jguillen-lab/BFS9000/firmware/vial-qmk/keyboards/jguillen_lab/bfs9000/readme.md

# BFS9000

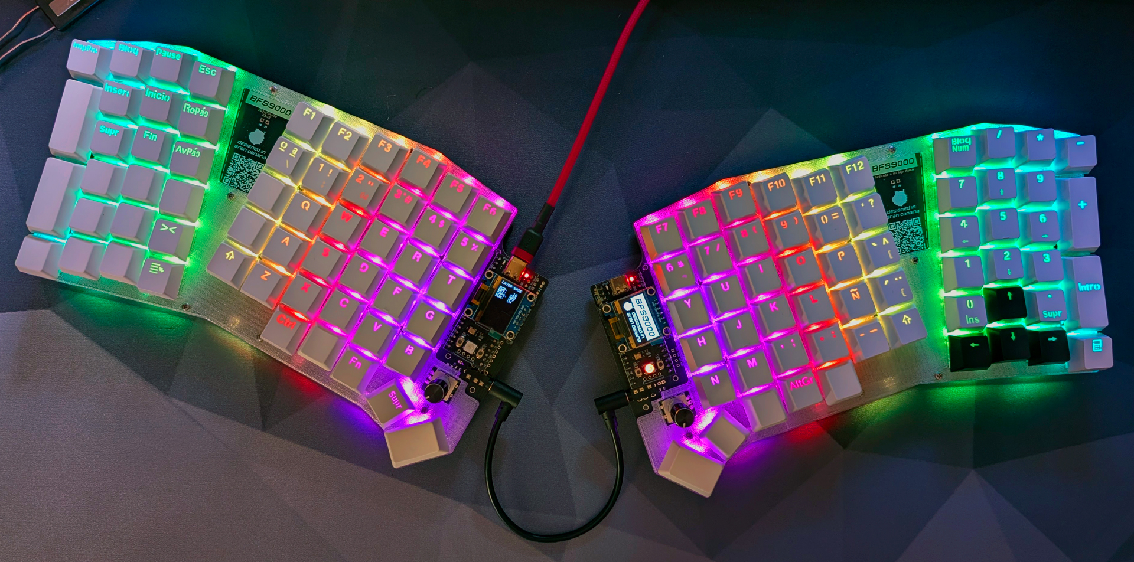
[picture p14: media/kbpic/000_no1.jpg]
BFS9000


BFS9000 is a custom split keyboard designed by Jesús Guillén. It runs QMK Firmware with Vial support and includes RGB Matrix lighting, OLED display support, combo/tap-dance features, and an Azoteq IQS5xx pointing device.

* Keyboard Maintainer: [Jesús Guillén](https://github.com/jguillen-lab)
* Hardware Supported: BFS9000 PCB
* Hardware Availability: [BFS9000 repository](https://github.com/jguillen-lab/BFS9000)

Make example for this keyboard, after setting up your build environment:

```
make jguillen_lab/bfs9000:default
```

Flashing example for this keyboard:

```
make jguillen_lab/bfs9000:default:flash
```

Vial keymap build example:

```
make jguillen_lab/bfs9000:vial
```

Vial keymap flashing example:

```
make jguillen_lab/bfs9000:vial:flash
```

See the [build environment setup](https://docs.qmk.fm/newbs_getting_started) and the [make instructions](https://docs.qmk.fm/newbs_building_firmware) for more information.
