jguillen-lab/BFS9000/media/keymap_es_ES.png

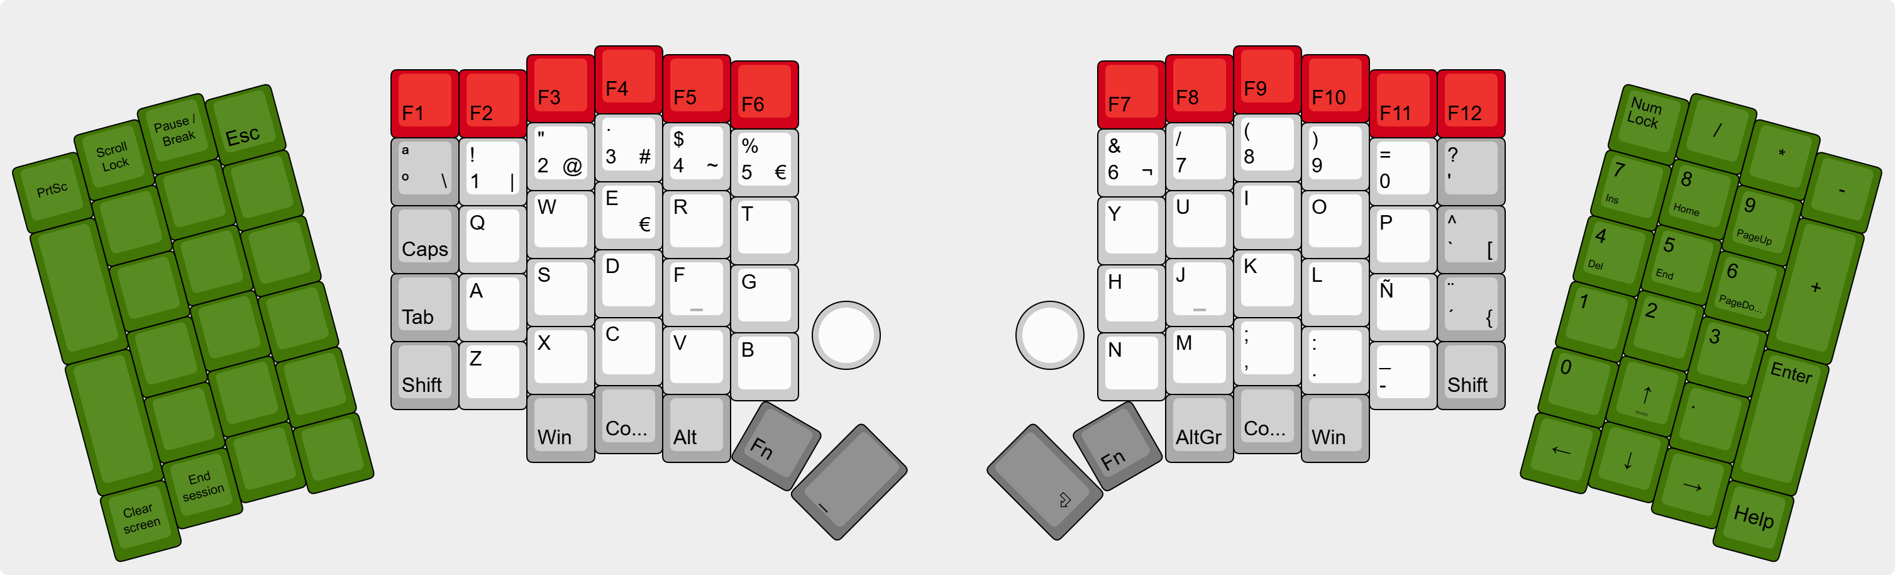
media/keymap_es_ES.png
