jguillen-lab/BFS9000/media/layouts/combinations.png

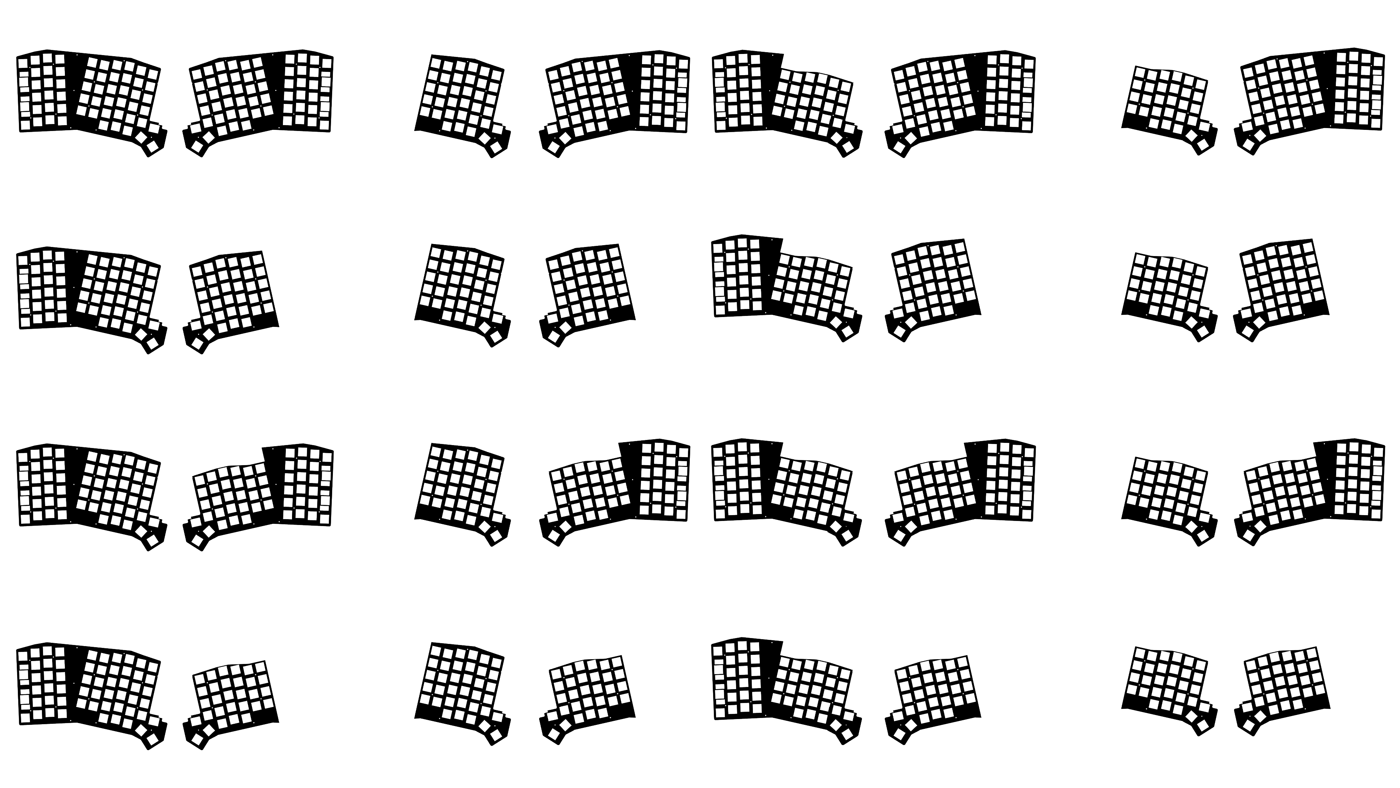
media/layouts/combinations.png
