jguillen-lab/BFS9000/media/layouts/full_left.png

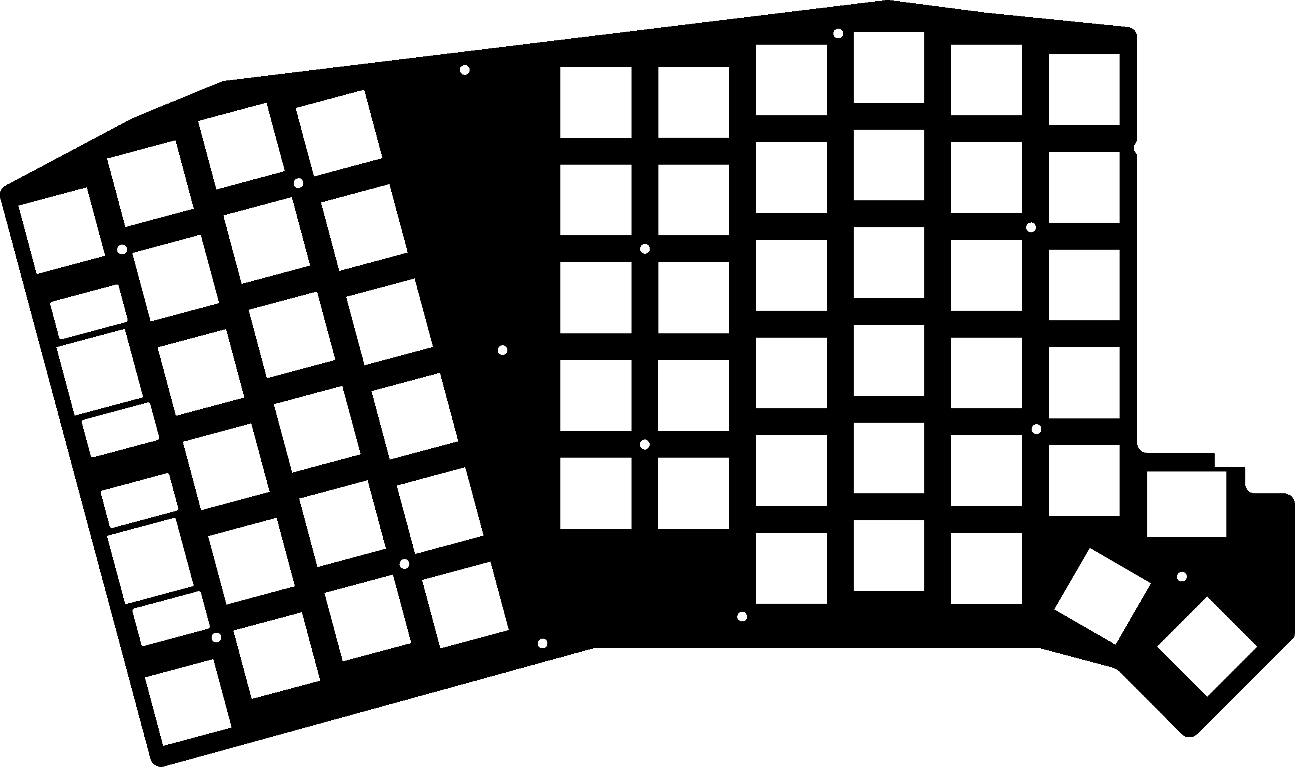
media/layouts/full_left.png
