jguillen-lab/BFS9000/media/layouts/full_right.png

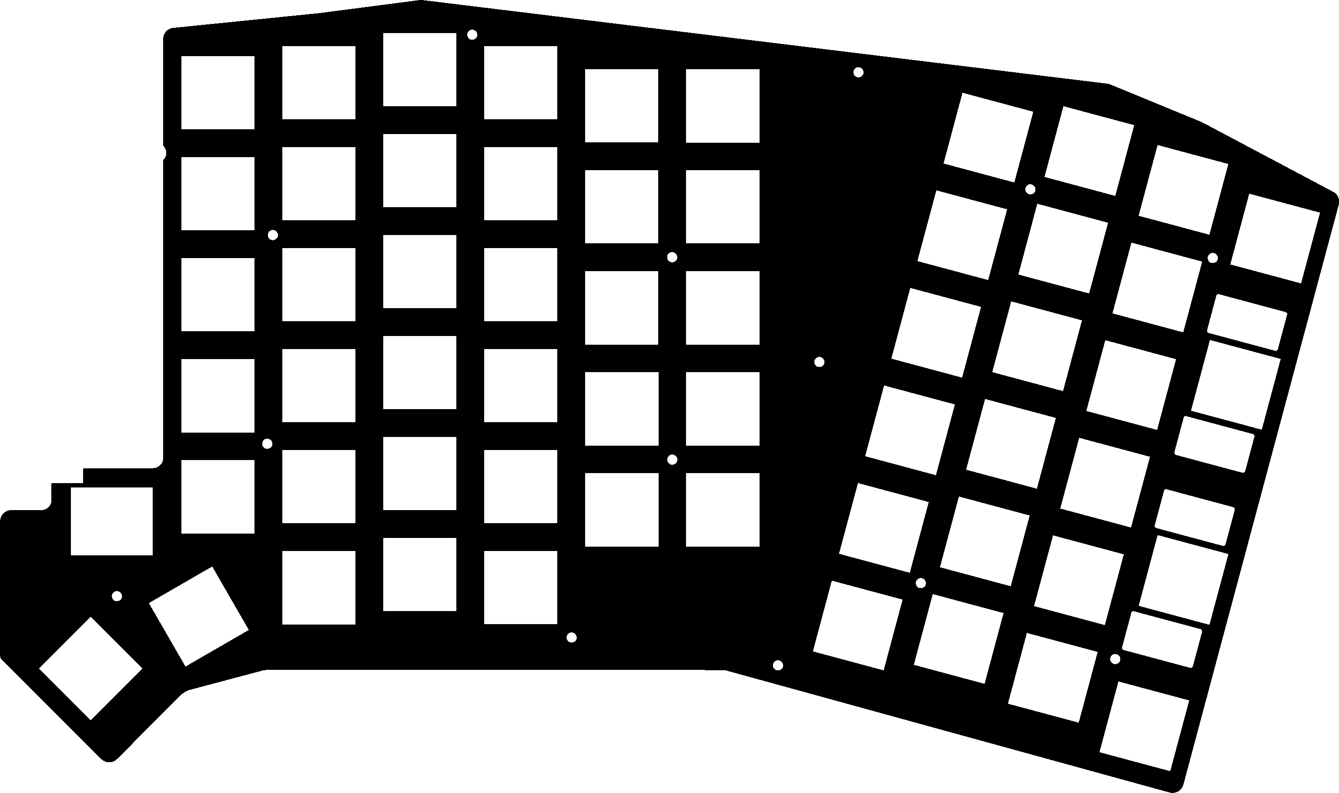
media/layouts/full_right.png
