jguillen-lab/BFS9000/media/layouts/main_left.png

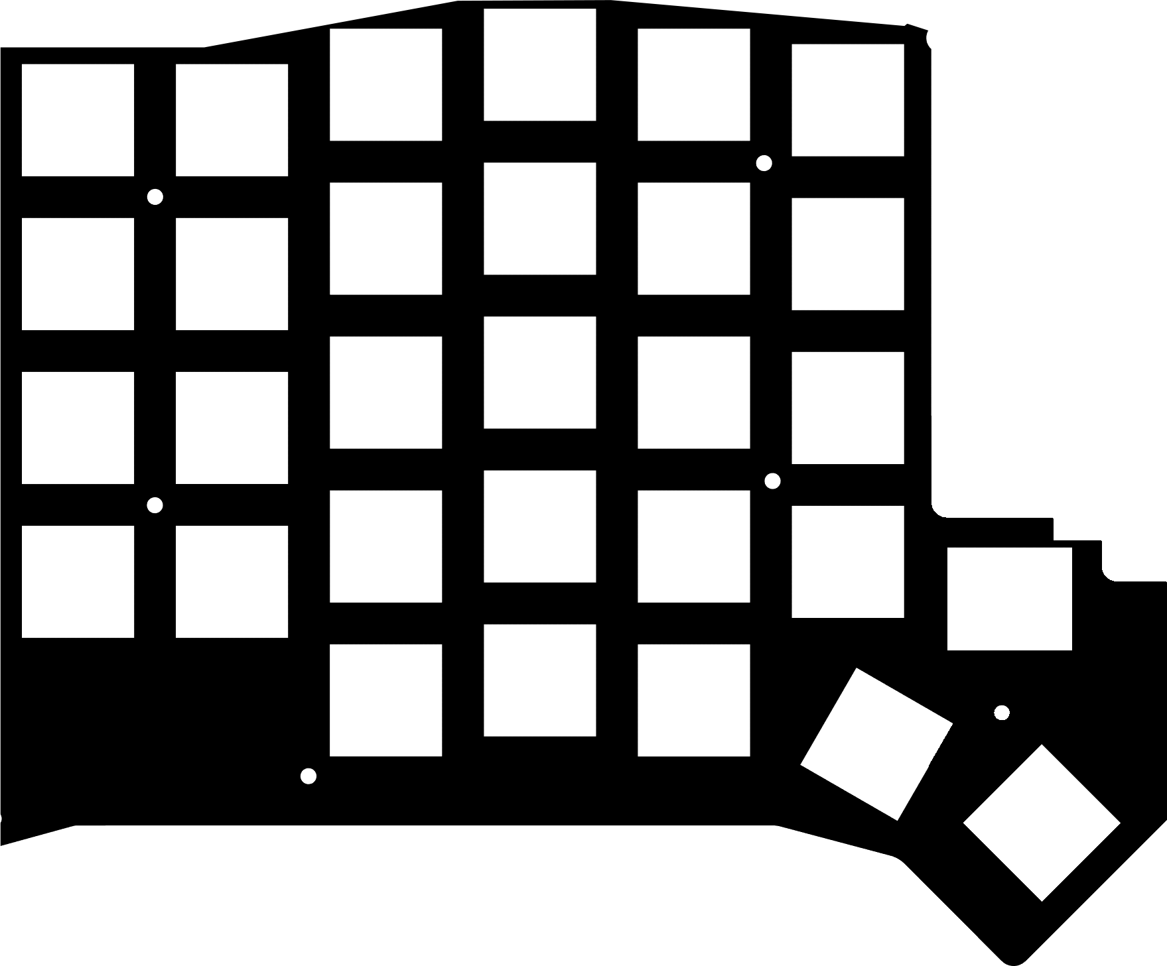
media/layouts/main_left.png
