jguillen-lab/BFS9000/media/layouts/main_right.png

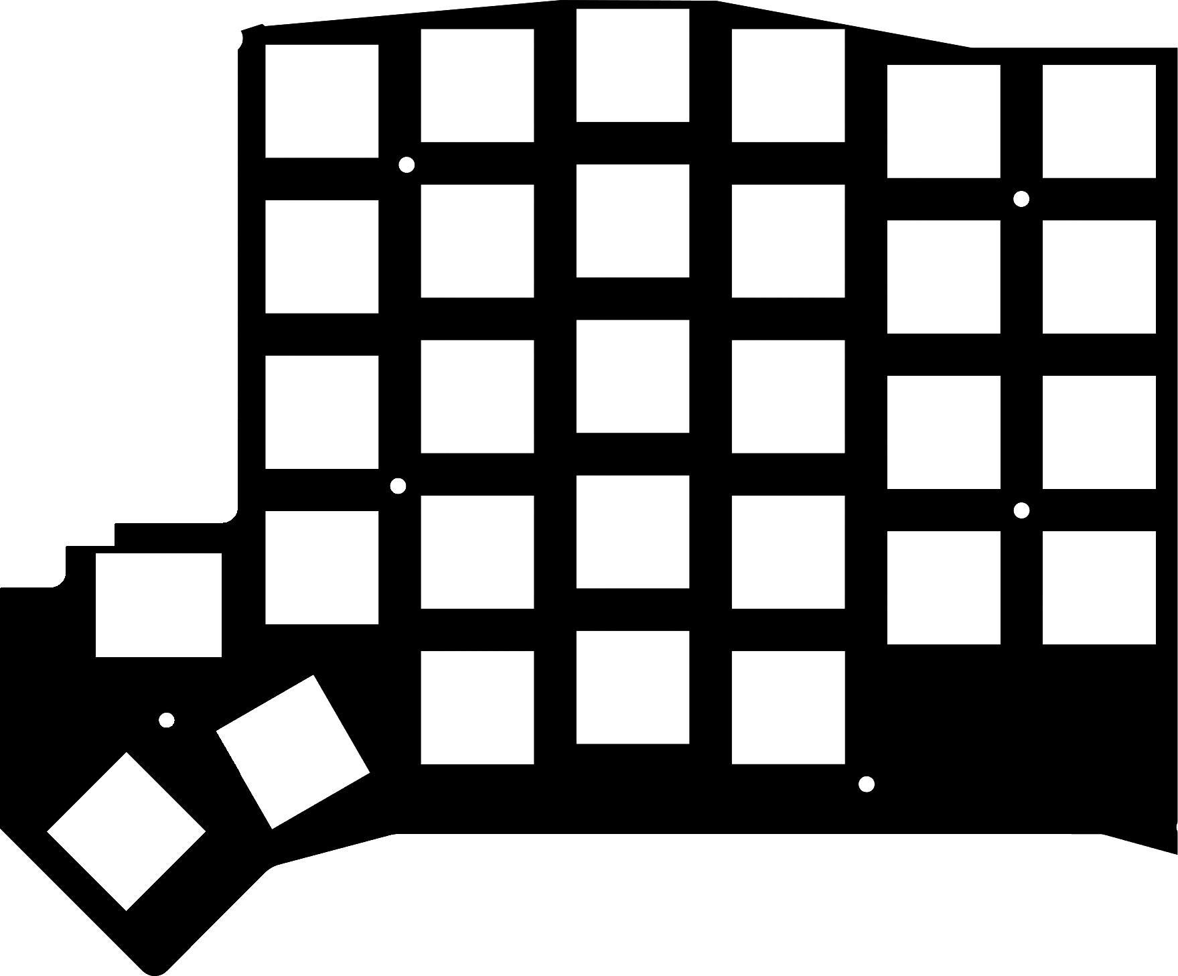
media/layouts/main_right.png
