jguillen-lab/BFS9000/media/layouts/main_side_right.png

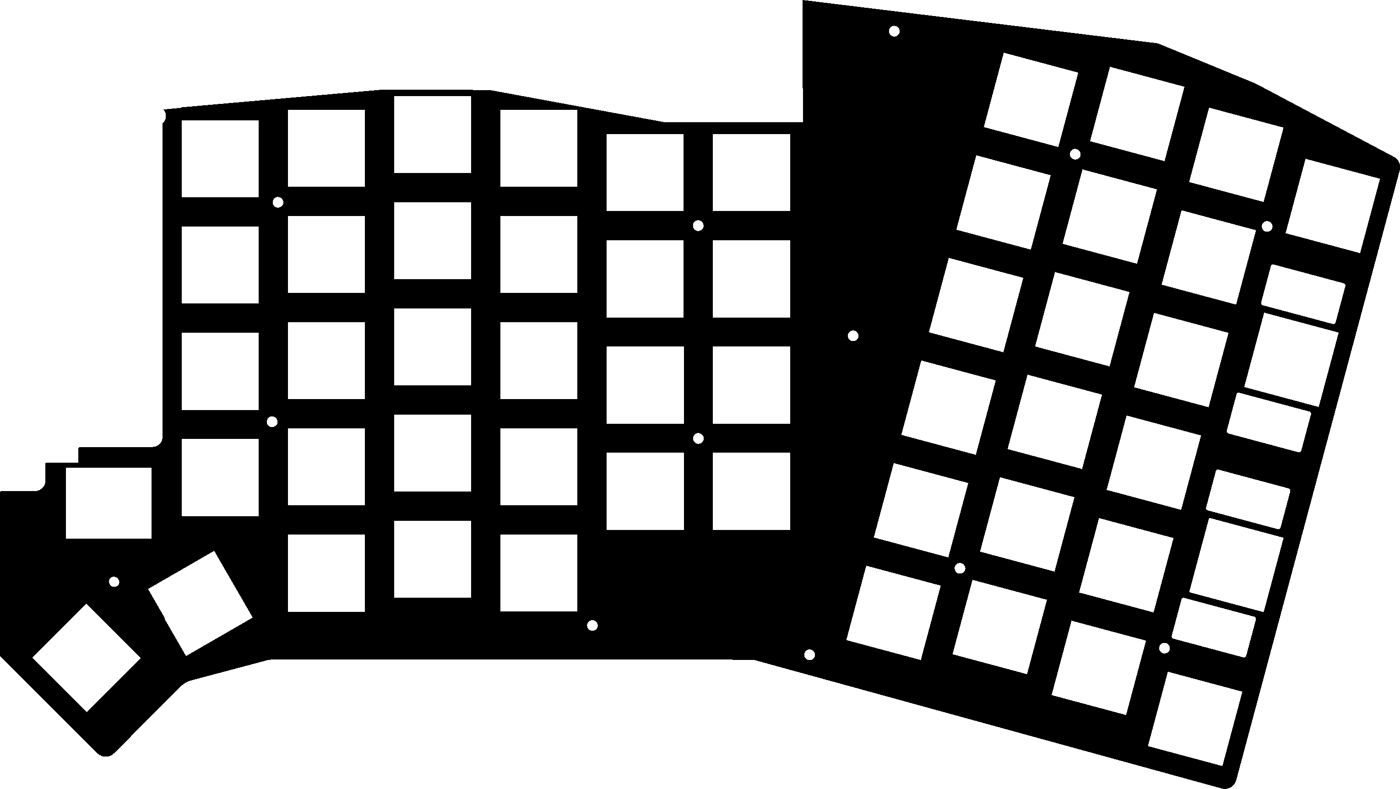
media/layouts/main_side_right.png
