jguillen-lab/BFS9000/media/layouts/main_top_left.png

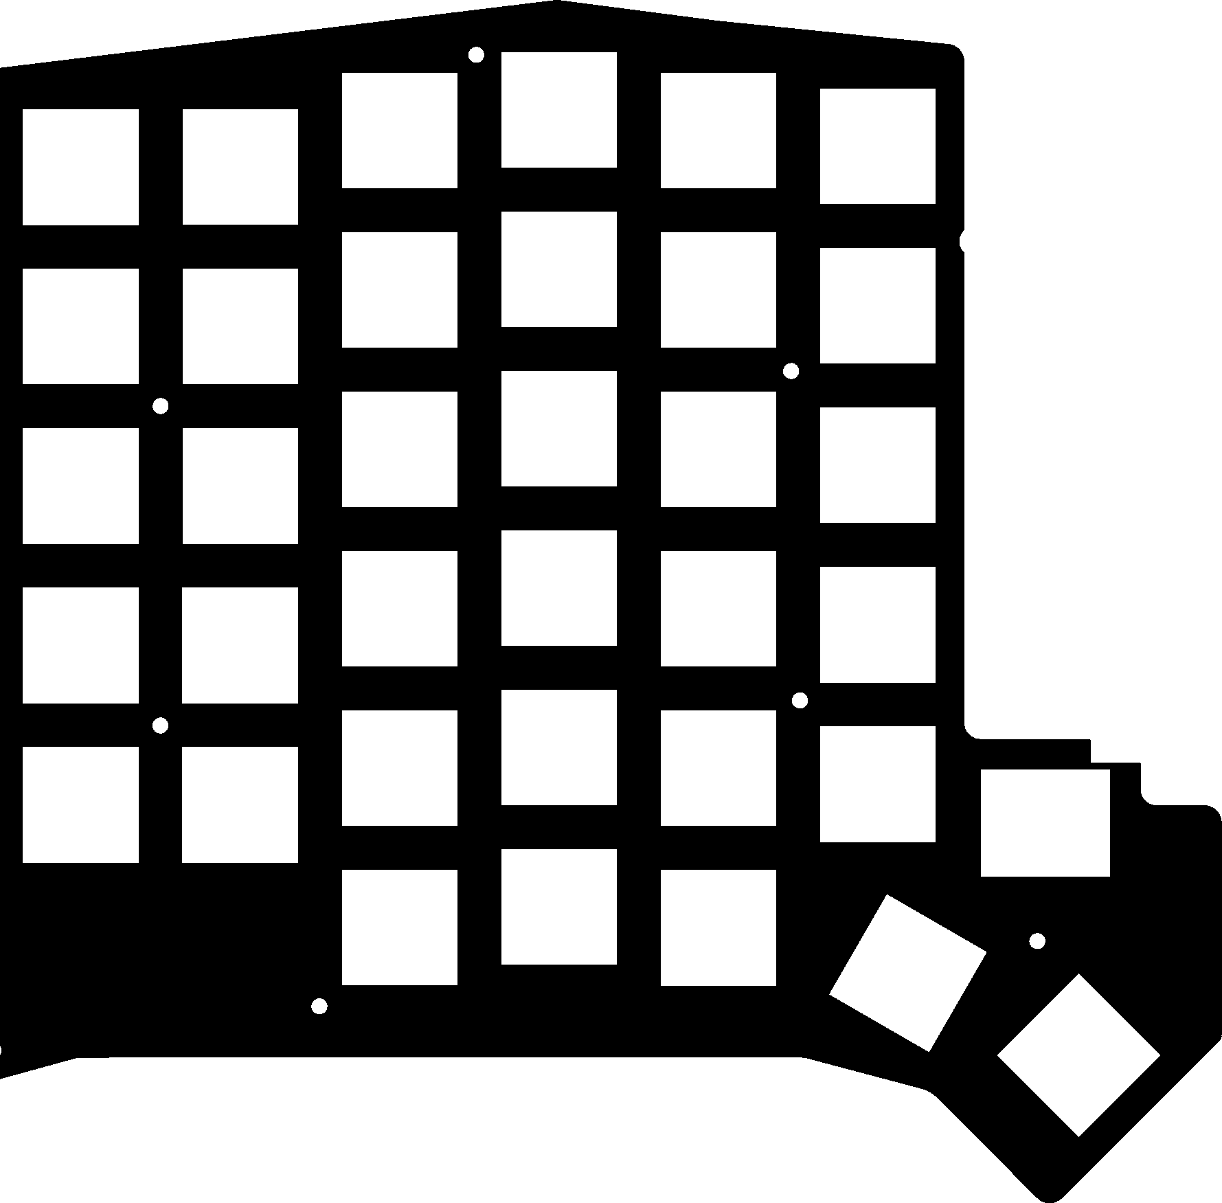
media/layouts/main_top_left.png
