jguillen-lab/BFS9000/media/layouts/main_top_right.png

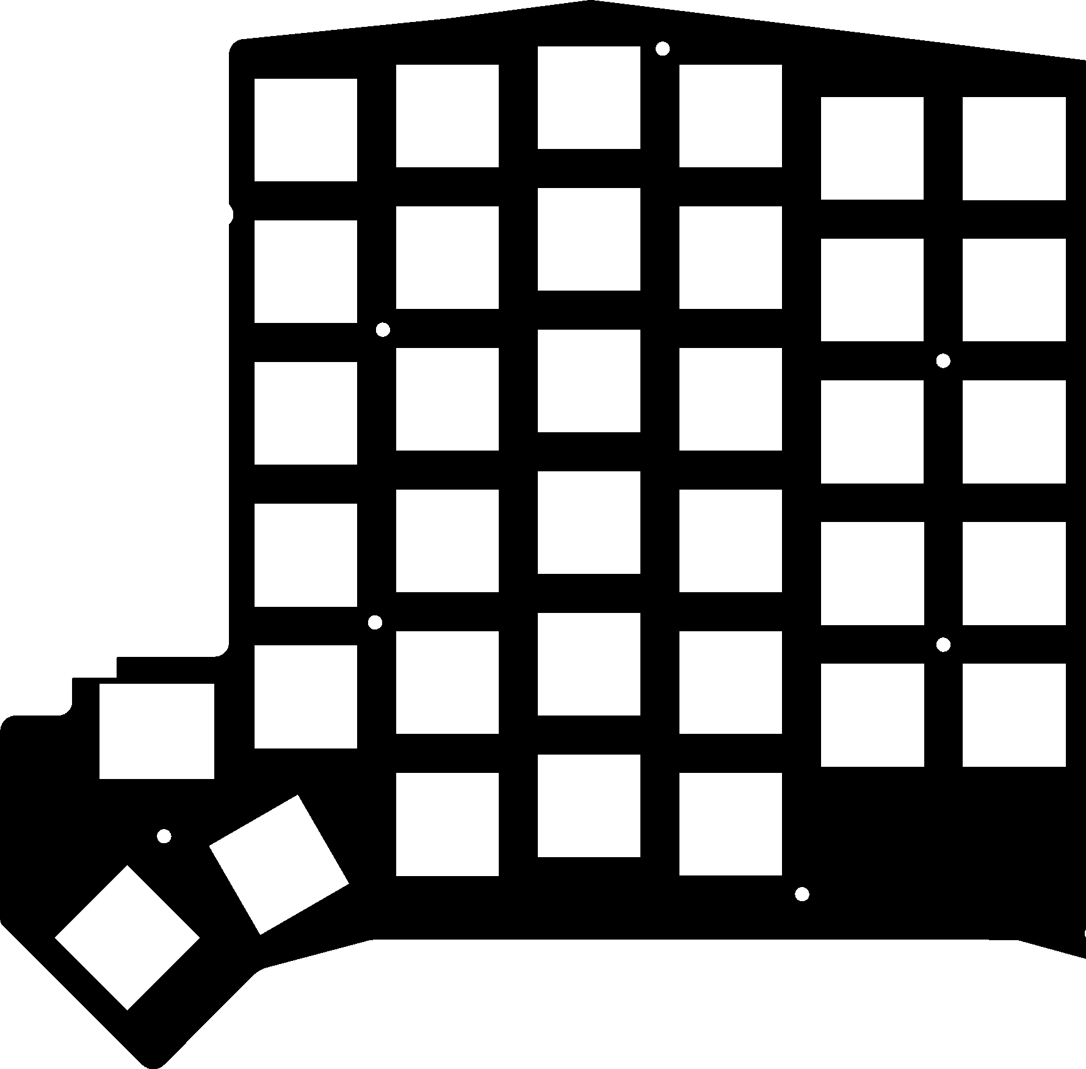
media/layouts/main_top_right.png
