jguillen-lab/BFS9000/hardware/enclosures/rev0.4/X_tps65_frame.3mf

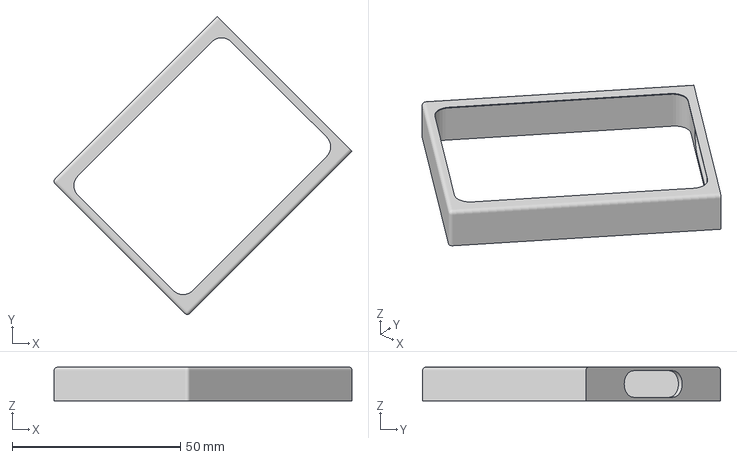
[picture p38: CAD file, 2026-06-24]
hardware/enclosures/rev0.4/X_tps65_frame.3mf
88.5 x 88.5 x 10.0 mm
