jguillen-lab/BFS9000/hardware/enclosures/rev0.4/X_tps65_bottom.3mf

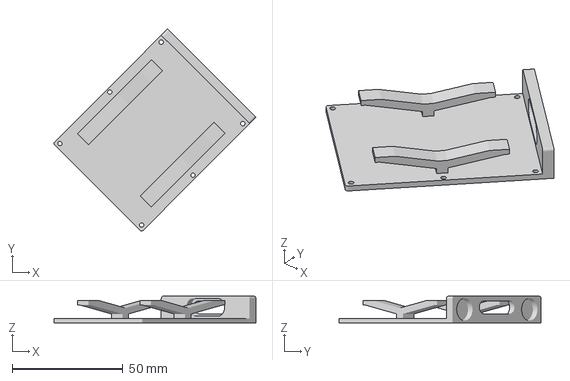
[picture p39: CAD file, 2026-06-24]
hardware/enclosures/rev0.4/X_tps65_bottom.3mf
91.3 x 91.3 x 12.0 mm
