jguillen-lab/BFS9000/firmware/vial-qmk/keyboards/jguillen_lab/bfs9000/keymaps/vial/config.h

/* SPDX-License-Identifier: GPL-2.0-or-later
 *
 * BFS9000 — Vial keymap configuration
 * Copyright (C) 2026 jguillen-lab
 *
 * This file is part of the BFS9000 / Marquichuelo keyboard firmware.
 * It is distributed under the terms of the GNU General Public License
 * version 2 or later.
 */

#pragma once

/* ─────────────────────────────────────────────────────────────────────────────
 * SPLIT USER TRANSACTIONS
 * ─────────────────────────────────────────────────────────────────────────────
 *
 * Reserves a user-defined split transaction ID for custom synchronisation
 * between halves. In this keymap it is used by the HELP/OLED state sync logic.
 */
#define SPLIT_TRANSACTION_IDS_USER USER_HELP_SYNC

/* ─────────────────────────────────────────────────────────────────────────────
 * SPLIT LED STATE
 * ─────────────────────────────────────────────────────────────────────────────
 *
 * Syncs host LED state such as Caps Lock / Num Lock between halves, so either
 * side can render lock indicators correctly.
 */
#define SPLIT_LED_STATE_ENABLE

/* ─────────────────────────────────────────────────────────────────────────────
 * VIAL KEYBOARD UID
 * ─────────────────────────────────────────────────────────────────────────────
 *
 * Unique 8-byte identifier used by Vial to distinguish this keyboard from any
 * other Vial device. Vial stores per-keyboard configuration indexed by this UID.
 *
 * Do not reuse the same UID on unrelated keyboards, otherwise Vial may treat
 * them as the same device and share/overwrite stored settings.
 */
#define VIAL_KEYBOARD_UID {0xBA, 0x74, 0x77, 0x3D, 0x18, 0xAF, 0xA6, 0x3D}

/* ─────────────────────────────────────────────────────────────────────────────
 * VIAL SECURITY UNLOCK COMBO
 * ─────────────────────────────────────────────────────────────────────────────
 *
 * Vial requires a physical key combo before allowing privileged operations from
 * the desktop app. The two arrays below are parallel lists of matrix positions:
 * ROWS[i] + COLS[i] identify each key in the unlock combo.
 *
 * Current combo:
 *   • row 0, col 0
 *   • row 4, col 6
 */
#define VIAL_UNLOCK_COMBO_ROWS { 0, 4 }
#define VIAL_UNLOCK_COMBO_COLS { 0, 6 }

/* ─────────────────────────────────────────────────────────────────────────────
 * RGB MATRIX / VIALRGB — PHYSICAL LED LAYOUT
 * ─────────────────────────────────────────────────────────────────────────────
 *
 * SK6812 MINI-E / WS2812-compatible LEDs.
 *
 * WS2812_DI_PIN
 *   Data pin for the LED chain.
 *
 * RGB_MATRIX_LED_COUNT
 *   Total number of addressable LEDs across both halves.
 *
 * RGB_MATRIX_SPLIT
 *   Per-half LED count. Keep this aligned with the physical chain order and
 *   with g_led_config in keymap.c.
 */
#define WS2812_DI_PIN GP0

#define RGB_MATRIX_LED_COUNT 124
#define RGB_MATRIX_SPLIT { 62, 62 }

/* ─────────────────────────────────────────────────────────────────────────────
 * RGB MATRIX / VIALRGB — DEFAULTS AND LIMITS
 * ─────────────────────────────────────────────────────────────────────────────
 *
 * RGB_MATRIX_MAXIMUM_BRIGHTNESS caps the highest brightness QMK will output.
 * RGB_MATRIX_DEFAULT_VAL is the startup brightness before EEPROM/Vial state is
 * restored. RGB_MATRIX_DEFAULT_MODE selects the initial effect.
 */
#define RGB_MATRIX_MAXIMUM_BRIGHTNESS 220
#define RGB_MATRIX_DEFAULT_VAL 64
#define RGB_MATRIX_DEFAULT_MODE RGB_MATRIX_SOLID_COLOR

/* ─────────────────────────────────────────────────────────────────────────────
 * RGB MATRIX — EFFECT SUPPORT
 * ─────────────────────────────────────────────────────────────────────────────
 *
 * These flags compile individual QMK RGB Matrix effects into the firmware.
 * VialRGB can only expose effects that are actually compiled here.
 *
 * RGB_MATRIX_KEYPRESSES enables reactive effects based on key activity.
 * RGB_MATRIX_FRAMEBUFFER_EFFECTS enables effects that need framebuffer support.
 */
#define RGB_MATRIX_KEYPRESSES
#define RGB_MATRIX_FRAMEBUFFER_EFFECTS

#define ENABLE_RGB_MATRIX_SOLID_COLOR
#define ENABLE_RGB_MATRIX_ALPHAS_MODS
#define ENABLE_RGB_MATRIX_GRADIENT_UP_DOWN
#define ENABLE_RGB_MATRIX_GRADIENT_LEFT_RIGHT
#define ENABLE_RGB_MATRIX_BREATHING

#define ENABLE_RGB_MATRIX_BAND_SAT
#define ENABLE_RGB_MATRIX_BAND_VAL
#define ENABLE_RGB_MATRIX_BAND_PINWHEEL_SAT
#define ENABLE_RGB_MATRIX_BAND_PINWHEEL_VAL
#define ENABLE_RGB_MATRIX_BAND_SPIRAL_SAT
#define ENABLE_RGB_MATRIX_BAND_SPIRAL_VAL

#define ENABLE_RGB_MATRIX_CYCLE_ALL
#define ENABLE_RGB_MATRIX_CYCLE_LEFT_RIGHT
#define ENABLE_RGB_MATRIX_CYCLE_UP_DOWN
#define ENABLE_RGB_MATRIX_RAINBOW_MOVING_CHEVRON
#define ENABLE_RGB_MATRIX_CYCLE_OUT_IN
#define ENABLE_RGB_MATRIX_CYCLE_OUT_IN_DUAL
#define ENABLE_RGB_MATRIX_CYCLE_PINWHEEL
#define ENABLE_RGB_MATRIX_CYCLE_SPIRAL
#define ENABLE_RGB_MATRIX_DUAL_BEACON
#define ENABLE_RGB_MATRIX_RAINBOW_BEACON
#define ENABLE_RGB_MATRIX_RAINBOW_PINWHEELS

#define ENABLE_RGB_MATRIX_RAINDROPS
#define ENABLE_RGB_MATRIX_JELLYBEAN_RAINDROPS
#define ENABLE_RGB_MATRIX_HUE_BREATHING
#define ENABLE_RGB_MATRIX_HUE_PENDULUM
#define ENABLE_RGB_MATRIX_HUE_WAVE
#define ENABLE_RGB_MATRIX_PIXEL_RAIN
#define ENABLE_RGB_MATRIX_PIXEL_FLOW
#define ENABLE_RGB_MATRIX_PIXEL_FRACTAL

#define ENABLE_RGB_MATRIX_TYPING_HEATMAP
#define ENABLE_RGB_MATRIX_DIGITAL_RAIN

#define ENABLE_RGB_MATRIX_SOLID_REACTIVE_SIMPLE
#define ENABLE_RGB_MATRIX_SOLID_REACTIVE
#define ENABLE_RGB_MATRIX_SOLID_REACTIVE_WIDE
#define ENABLE_RGB_MATRIX_SOLID_REACTIVE_MULTIWIDE
#define ENABLE_RGB_MATRIX_SOLID_REACTIVE_CROSS
#define ENABLE_RGB_MATRIX_SOLID_REACTIVE_MULTICROSS
#define ENABLE_RGB_MATRIX_SOLID_REACTIVE_NEXUS
#define ENABLE_RGB_MATRIX_SOLID_REACTIVE_MULTINEXUS
#define ENABLE_RGB_MATRIX_SPLASH
#define ENABLE_RGB_MATRIX_MULTISPLASH
#define ENABLE_RGB_MATRIX_SOLID_SPLASH
#define ENABLE_RGB_MATRIX_SOLID_MULTISPLASH

/* ─────────────────────────────────────────────────────────────────────────────
 * TPS65 / AZOTEQ IQS5XX TRACKPAD
 * ─────────────────────────────────────────────────────────────────────────────
 *
 * AZOTEQ_IQS5XX_TPS65 selects the TPS65 hardware profile for the Azoteq IQS5xx
 * pointing-device driver.
 *
 * SPLIT_POINTING_ENABLE enables pointing-device support in a split keyboard.
 * POINTING_DEVICE_RIGHT declares that the pointing device is physically on the
 * right half.
 */
#define AZOTEQ_IQS5XX_TPS65
#define SPLIT_POINTING_ENABLE
#define POINTING_DEVICE_RIGHT
