jguillen-lab/BFS9000/software/MARCOntroller/src/agent/mod.rs

// ============================================================================
// src/agent/mod.rs — Agent runtime modules
// ============================================================================
//
// MIT License — Copyright (c) 2026 Jesús Guillén (jguillen-lab)
//
// ============================================================================

pub mod mqtt;
pub mod runtime;
